testlogger/tl-collector-3d-print-files/main-units/TL0101001-collector-mini/TL0201002-case.stl

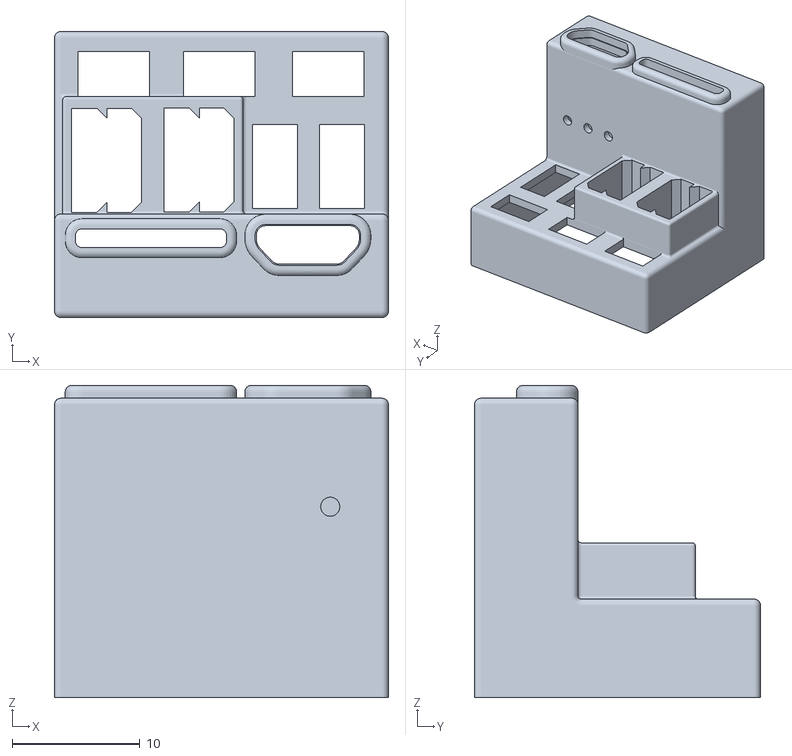
[picture p22: CAD file, 2021-08-22]
main-units/TL0101001-collector-mini/TL0201002-case.stl
26.1 x 22.4 x 24.4
